KP1533TM2/e003-capstan/hw/rev1/img/hot.jpg

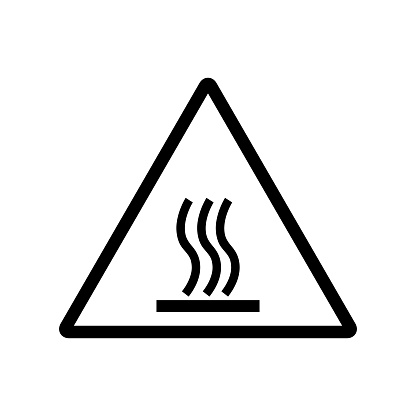
hw/rev1/img/hot.jpg
