KP1533TM2/e003-capstan/soft/Motor.ini

[General]
WindowState=0
Left=527
Top=113
Width=800
Height=790
DataDir=D:\Projects\NSM_lab\Audio\E-004\Capstan\Soft\Data\
Port=33
ShowG1=1
ShowG2=1
ShowG3=1
ShowG4=0
ShowG5=0
ShowG6=0

[Settings]
AutoConnect=0
AutoRead=1
Sample=100
AutoScroll=1

[Colours]
Background=16777215
Axis=13948116
Text=4737096
Cursor=0
Graph1=32768
Graph2=255
Graph3=4227327
Graph4=16711680
Graph5=4259584
Graph6=12615935

[Params]
Diameter=6
Thickness=35
Slip=0.69
Poles=112
