KP1533TM2/e003-capstan/soft/Motor.cpp

//---------------------------------------------------------------------------
#include <vcl.h>
#pragma hdrstop
#include "Main.h"
//---------------------------------------------------------------------------
USEFORM("Connect.cpp", ConnectForm);
USEFORM("Colours.cpp", ColoursForm);
USEFORM("About.cpp", AboutForm);
USEFORM("Settings.cpp", SettingsForm);
USEFORM("Main.cpp", MainForm);
//---------------------------------------------------------------------------
WINAPI WinMain(HINSTANCE, HINSTANCE, LPSTR, int)
{
  try
  {
     Application->Initialize();
     Application->Title = SOFTNAME;
     Application->CreateForm(__classid(TMainForm), &MainForm);
     Application->Run();
  }
  catch (Exception &exception)
  {
     Application->ShowException(&exception);
  }
  catch (...)
  {
     try
     {
       throw Exception("");
     }
     catch (Exception &exception)
     {
       Application->ShowException(&exception);
     }
  }
  return 0;
}
//---------------------------------------------------------------------------
