KP1533TM2/e003-capstan/soft/About.h

//---------------------------------------------------------------------------

#ifndef AboutH
#define AboutH
//---------------------------------------------------------------------------
#include <Classes.hpp>
#include <Controls.hpp>
#include <StdCtrls.hpp>
#include <Forms.hpp>
#include <ExtCtrls.hpp>
#include <Graphics.hpp>
//---------------------------------------------------------------------------
class TAboutForm : public TForm
{
__published:	// IDE-managed Components
  TPanel *Panel1;
  TImage *Image1;
  TImage *Image2;
  TLabel *Label1;
  TLabel *Label2;
  TButton *Button1;
  TLabel *Label3;
  void __fastcall Button1Click(TObject *Sender);
  void __fastcall FormClose(TObject *Sender, TCloseAction &Action);
  void __fastcall FormKeyPress(TObject *Sender, char &Key);
  void __fastcall FormCreate(TObject *Sender);
private:	// User declarations
public:		// User declarations
  __fastcall TAboutForm(TComponent* Owner);
};
//---------------------------------------------------------------------------
extern PACKAGE TAboutForm *AboutForm;
//---------------------------------------------------------------------------
#endif
